thisoldgeek/Modern-Jukebox/images/Modern-Jukebox-Small.gif

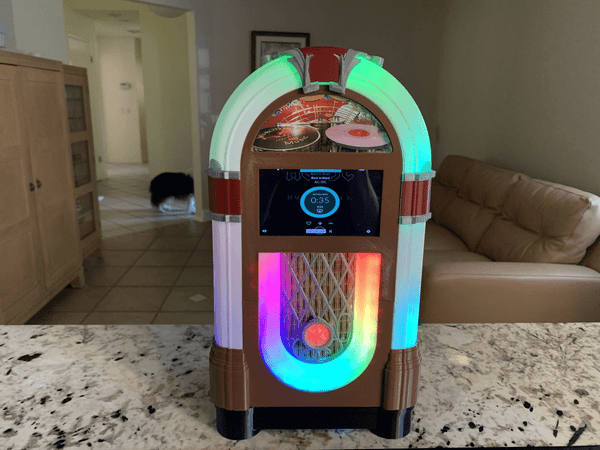
images/Modern-Jukebox-Small.gif
