thisoldgeek/Modern-Jukebox/STL-files/CaseRight.stl

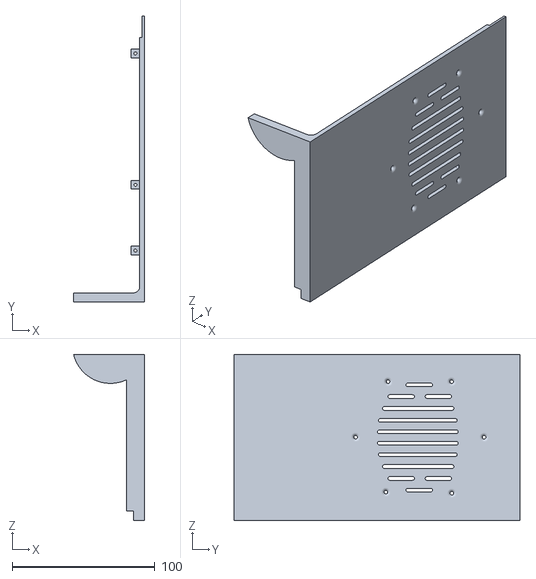
[picture p38: CAD file, 2021-02-26]
STL-files/CaseRight.stl
49.6 x 200.0 x 116.2
