thisoldgeek/Modern-Jukebox/STL-files/GrilleTube.stl

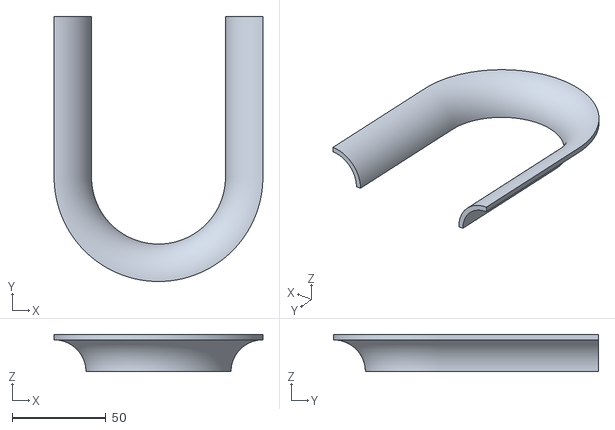
[picture p39: CAD file, 2021-02-26]
STL-files/GrilleTube.stl
111.5 x 141.5 x 20.0
