thisoldgeek/Modern-Jukebox/STL-files/BaseWithSwitches.stl

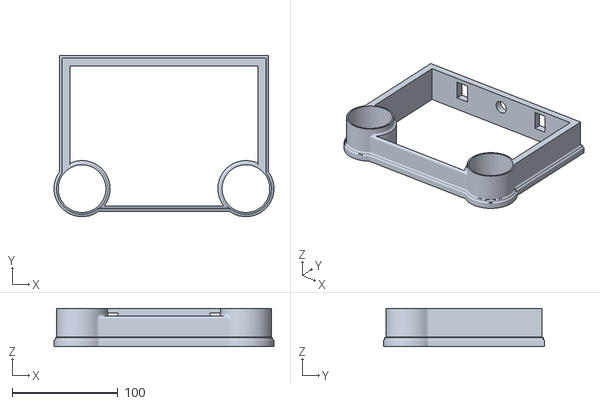
[picture p40: CAD file, 2021-02-26]
STL-files/BaseWithSwitches.stl
207.9 x 152.6 x 36.0
