thisoldgeek/Modern-Jukebox/STL-files/GrilleLEDHolder.stl

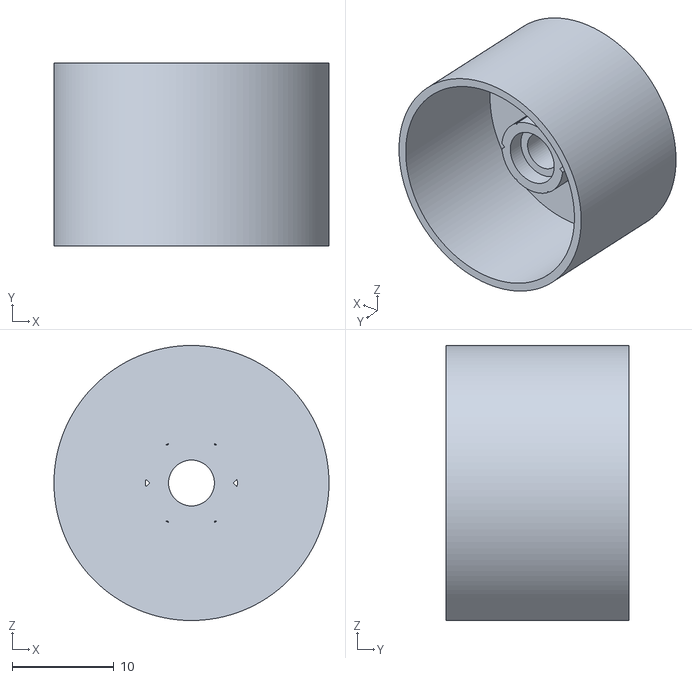
[picture p41: CAD file, 2021-02-26]
STL-files/GrilleLEDHolder.stl
27.0 x 18.0 x 27.0
