thisoldgeek/Modern-Jukebox/3D-Prints/Arch.png

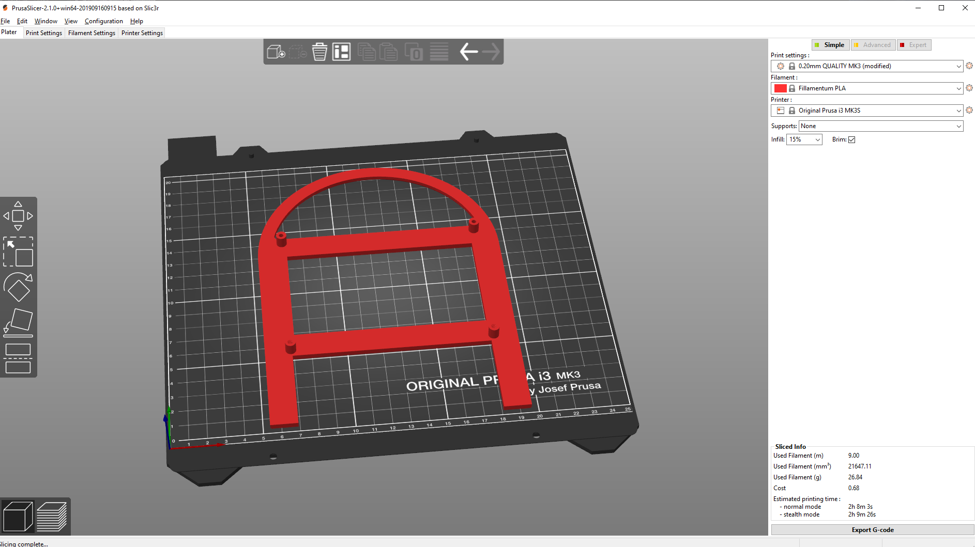
3D-Prints/Arch.png
