thisoldgeek/Modern-Jukebox/3D-Prints/BackCoverBottom.png

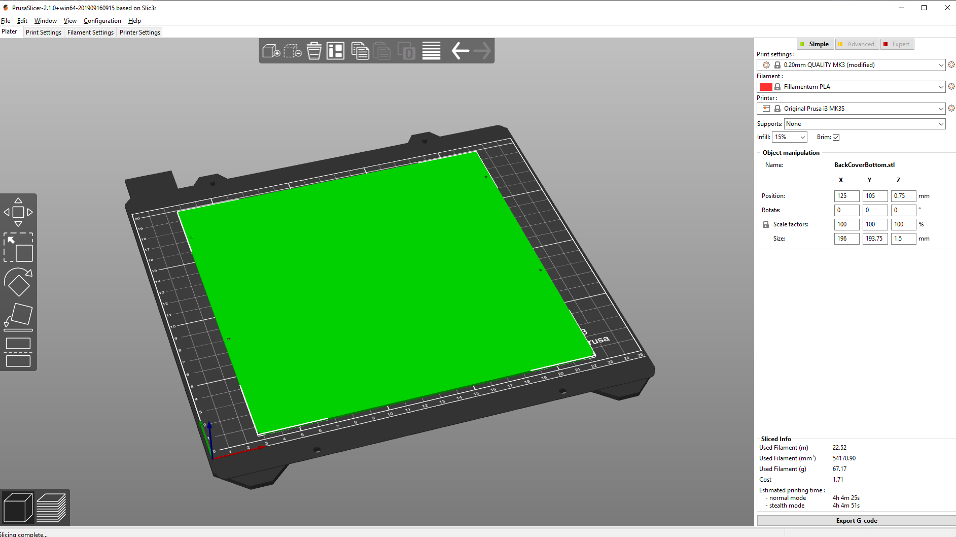
3D-Prints/BackCoverBottom.png
