thisoldgeek/Modern-Jukebox/3D-Prints/BaseWithSwitches.png

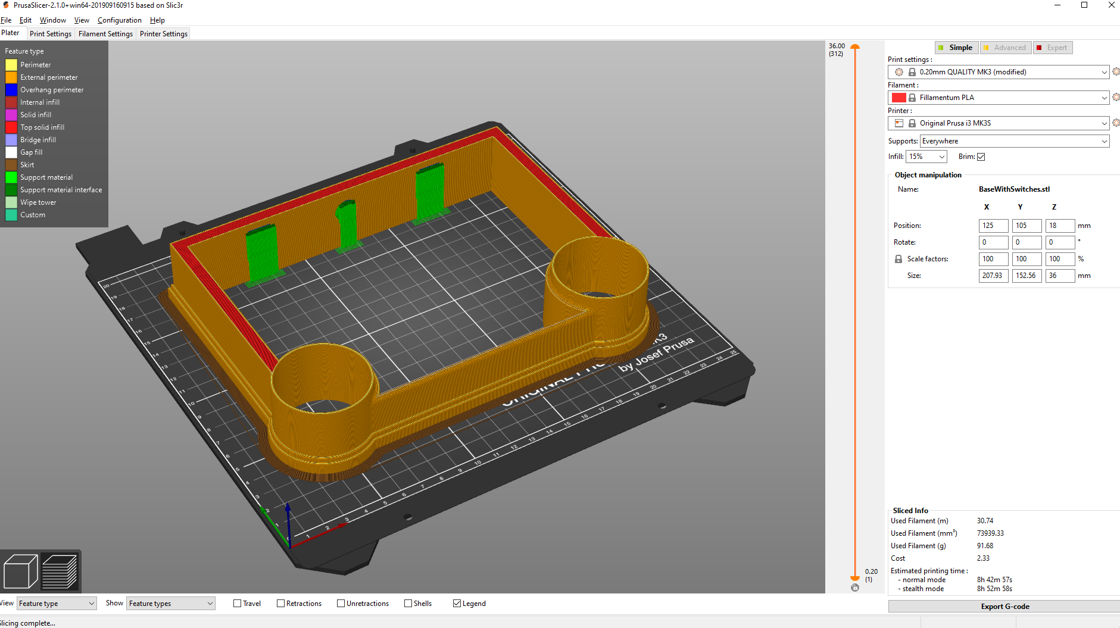
3D-Prints/BaseWithSwitches.png
