thisoldgeek/Modern-Jukebox/3D-Prints/CaseArch.png

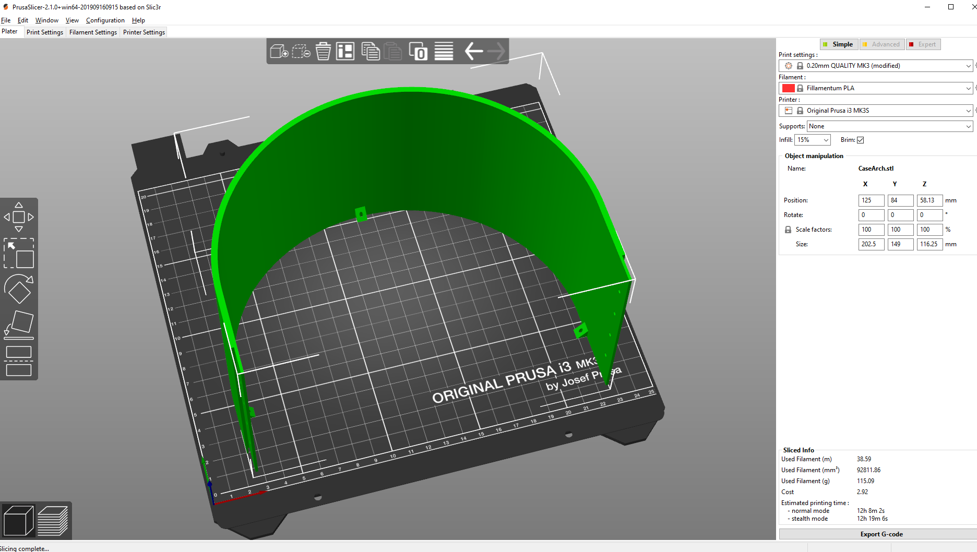
3D-Prints/CaseArch.png
