thisoldgeek/Modern-Jukebox/3D-Prints/CaseJointCover.png

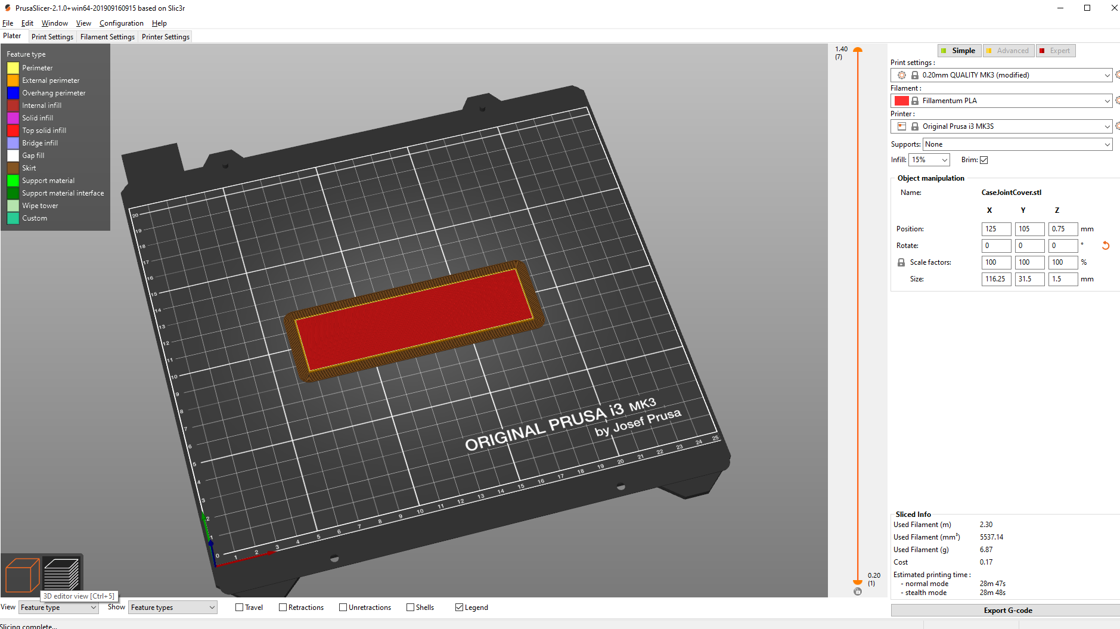
3D-Prints/CaseJointCover.png
