thisoldgeek/Modern-Jukebox/3D-Prints/Grille.png

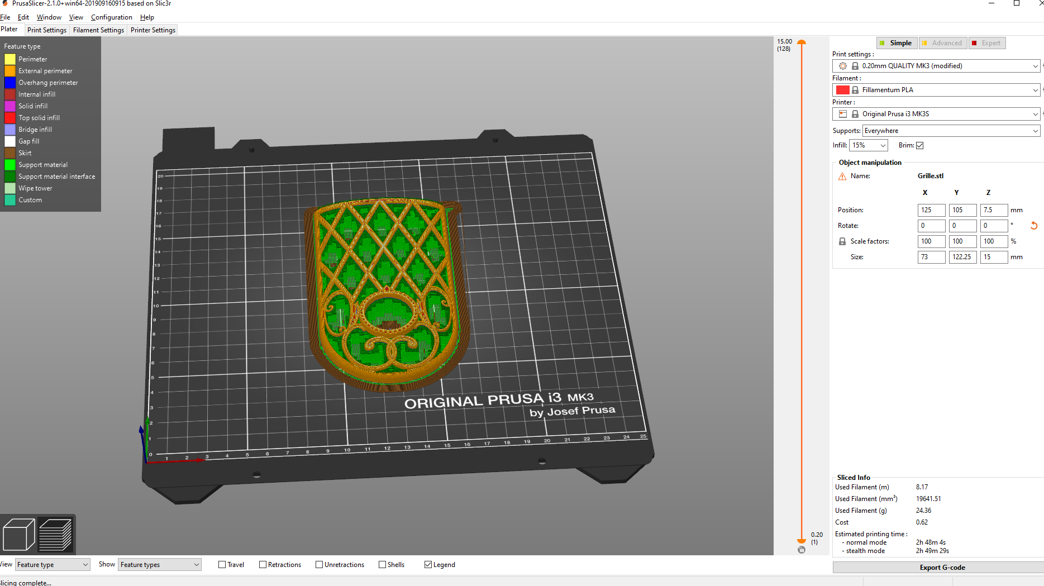
3D-Prints/Grille.png
