thisoldgeek/Modern-Jukebox/3D-Prints/GrilleLight.png

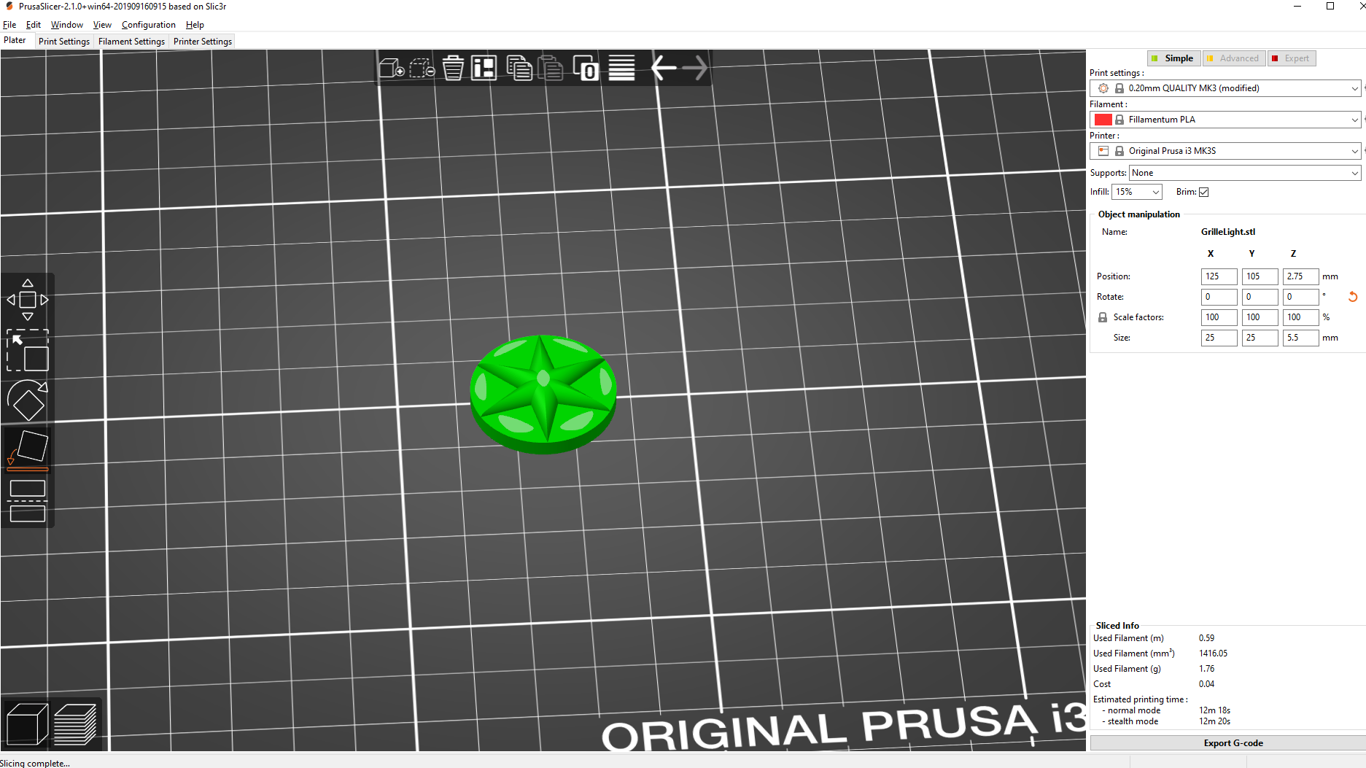
3D-Prints/GrilleLight.png
