thisoldgeek/Modern-Jukebox/3D-Prints/GrilleTube.png

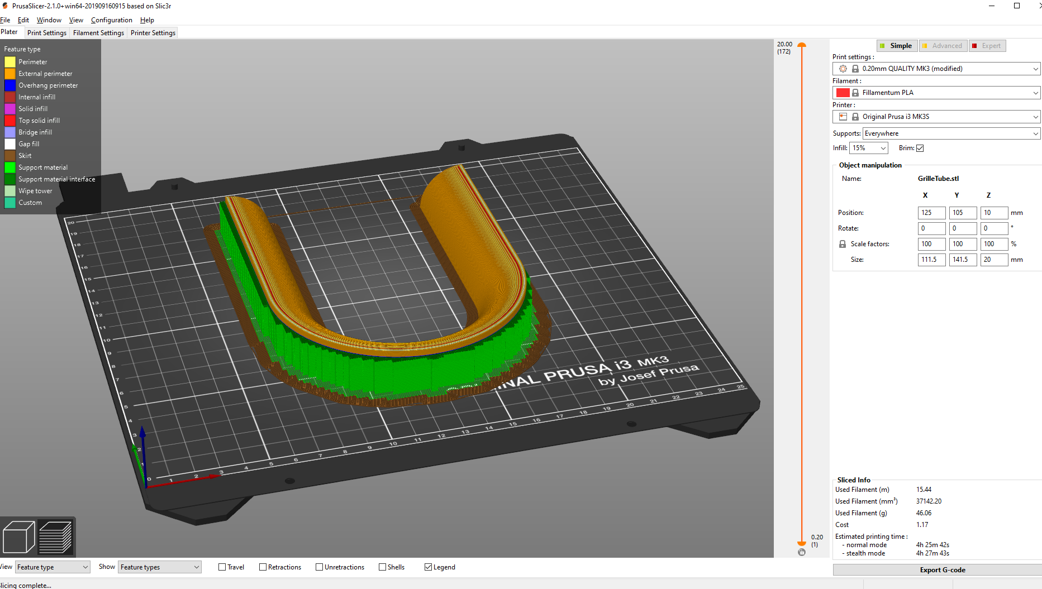
3D-Prints/GrilleTube.png
