thisoldgeek/Modern-Jukebox/3D-Prints/Neon1Arch.png

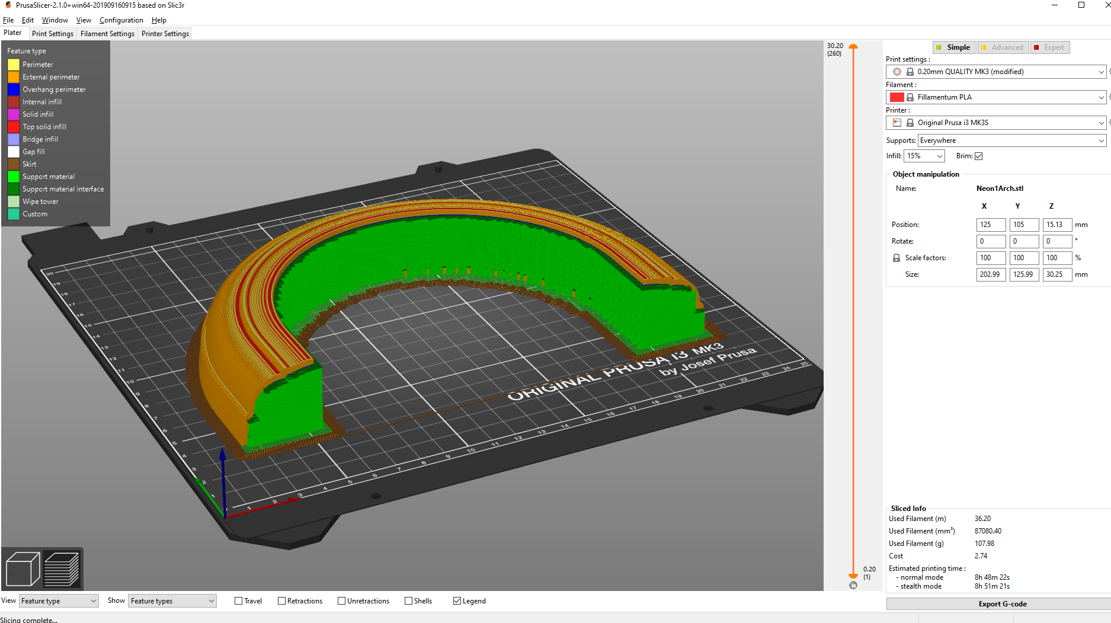
3D-Prints/Neon1Arch.png
