thisoldgeek/Modern-Jukebox/3D-Prints/Neon2Tubes.png

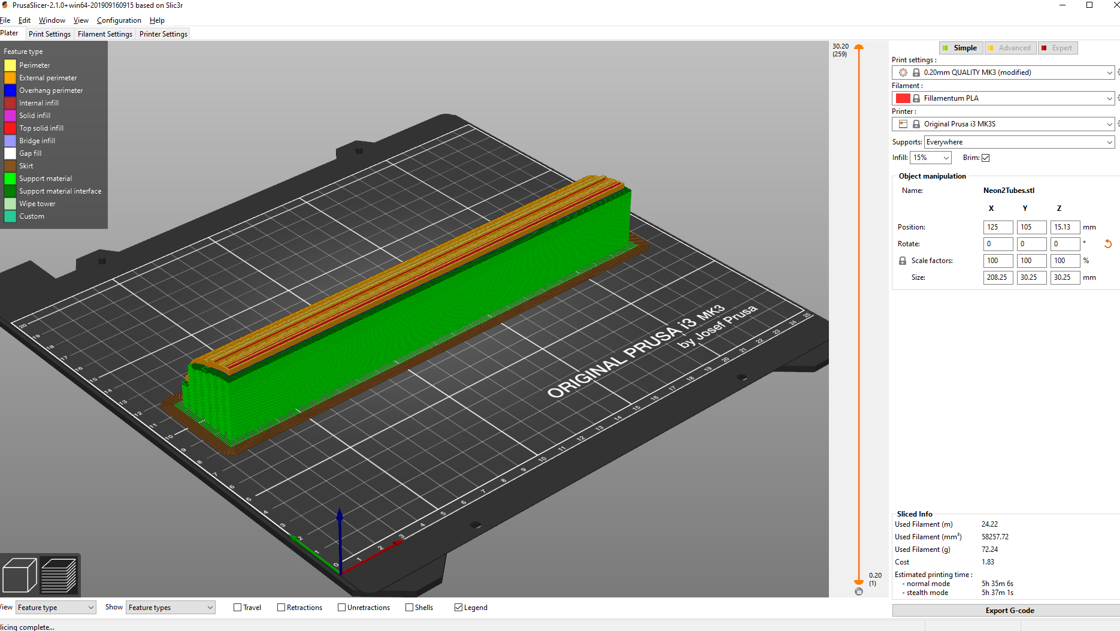
3D-Prints/Neon2Tubes.png
