thisoldgeek/Modern-Jukebox/3D-Prints/NeonTubeFanDecoration.png

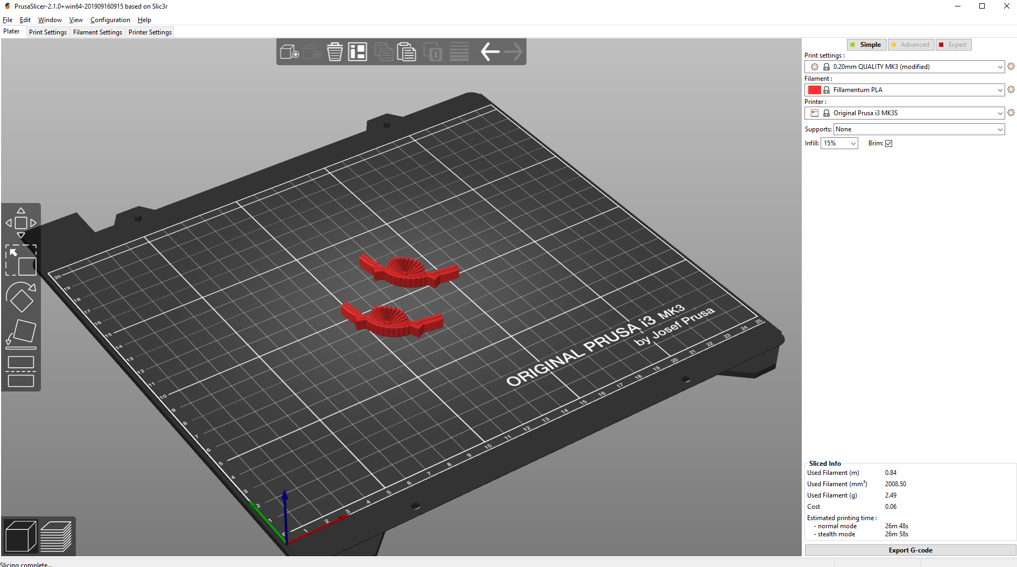
3D-Prints/NeonTubeFanDecoration.png
