thisoldgeek/Modern-Jukebox/3D-Prints/NeonTubeOrnament.png

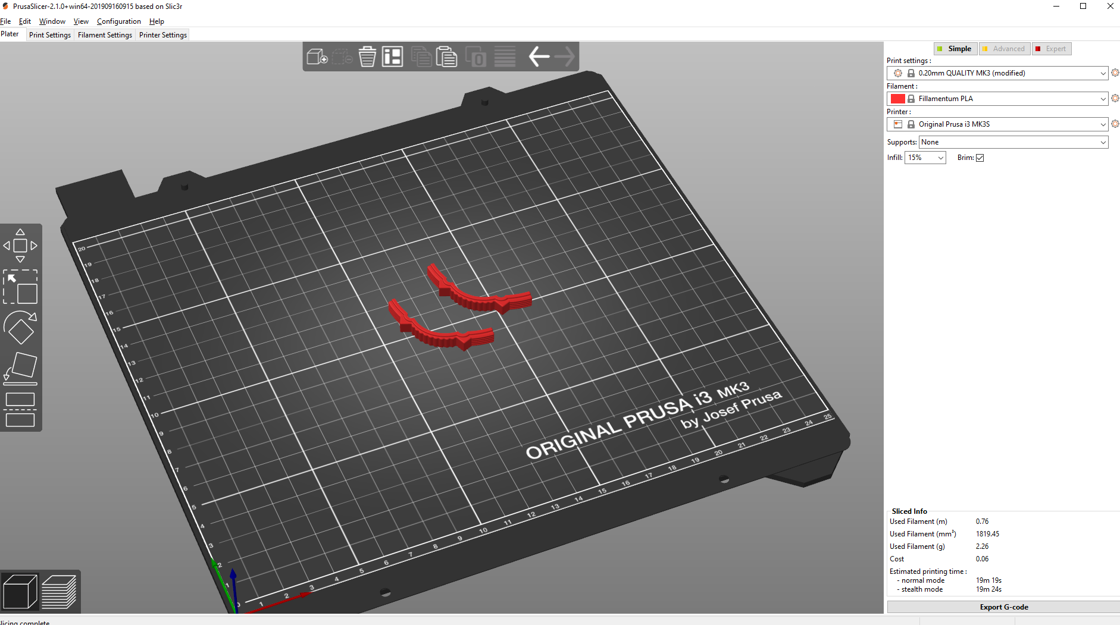
3D-Prints/NeonTubeOrnament.png
