thisoldgeek/Modern-Jukebox/3D-Prints/TopOrnament.png

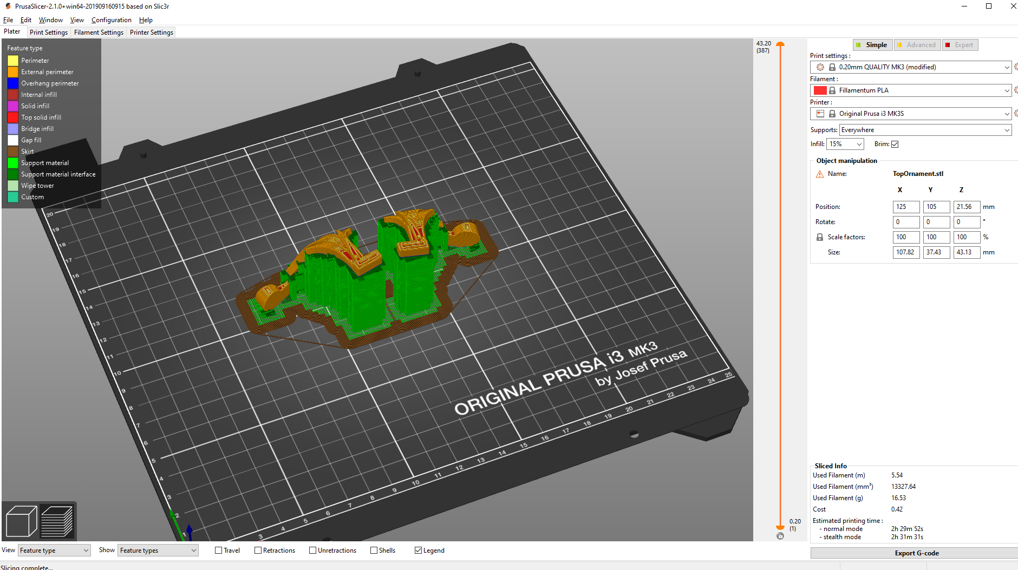
3D-Prints/TopOrnament.png
